techy-robot/CACKLE/Docs/Wiki/media/ESP32-S3.png

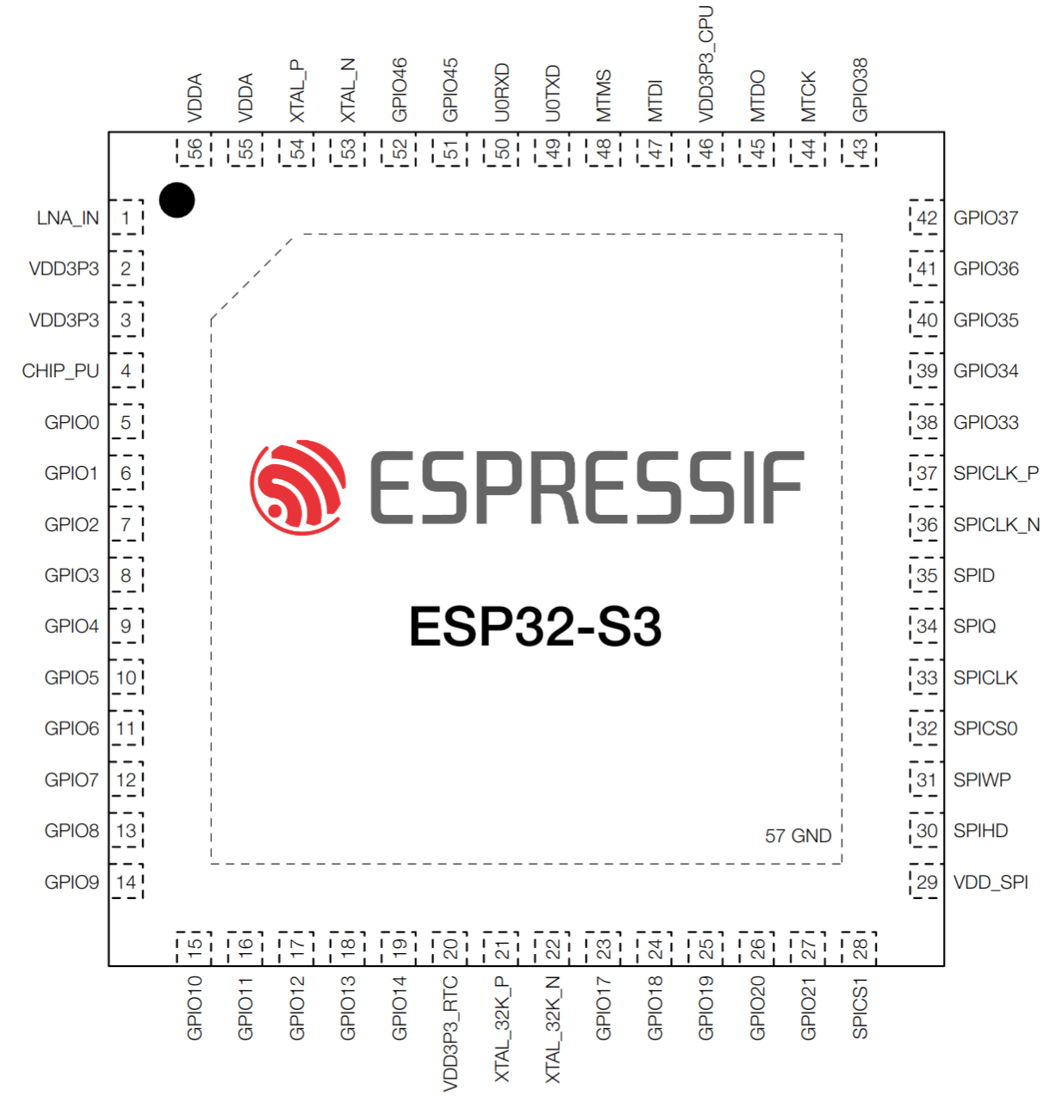
Docs/Wiki/media/ESP32-S3.png
