techy-robot/CACKLE/Docs/Wiki/media/STM32G0B1KCUx.jpg

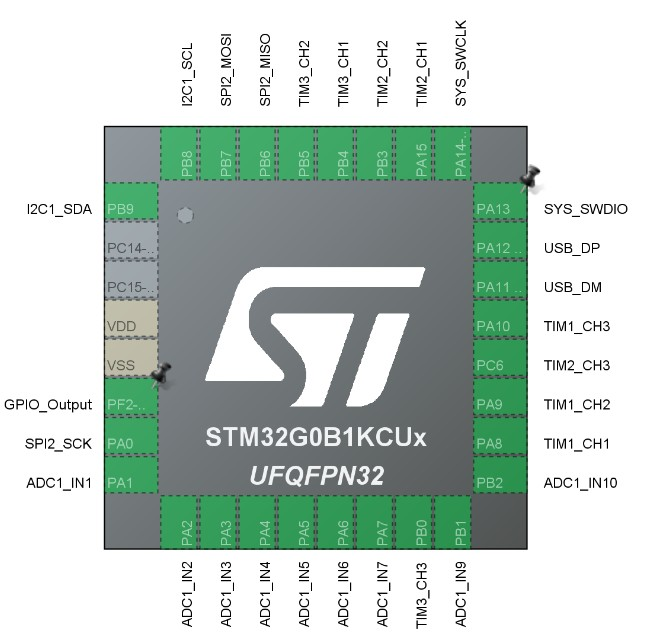
Docs/Wiki/media/STM32G0B1KCUx.jpg
