techy-robot/CACKLE/Docs/Wiki/media/STM32G070CB.jpg

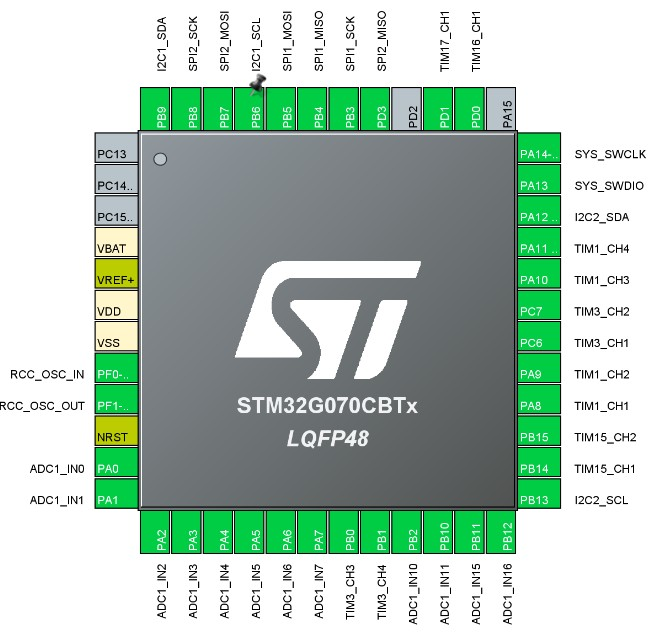
Docs/Wiki/media/STM32G070CB.jpg
