techy-robot/CACKLE/Docs/Wiki/media/STM32G070KB.jpg

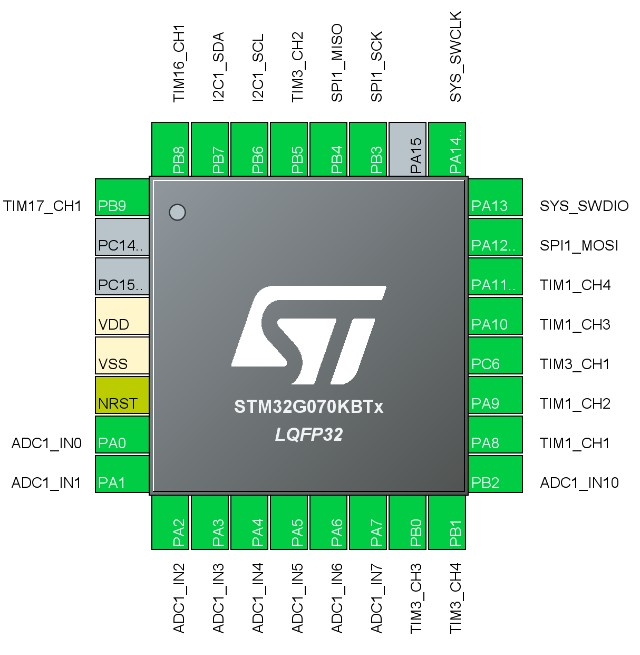
Docs/Wiki/media/STM32G070KB.jpg
