techy-robot/CACKLE/Docs/Wiki/media/STM32G473CB.jpg

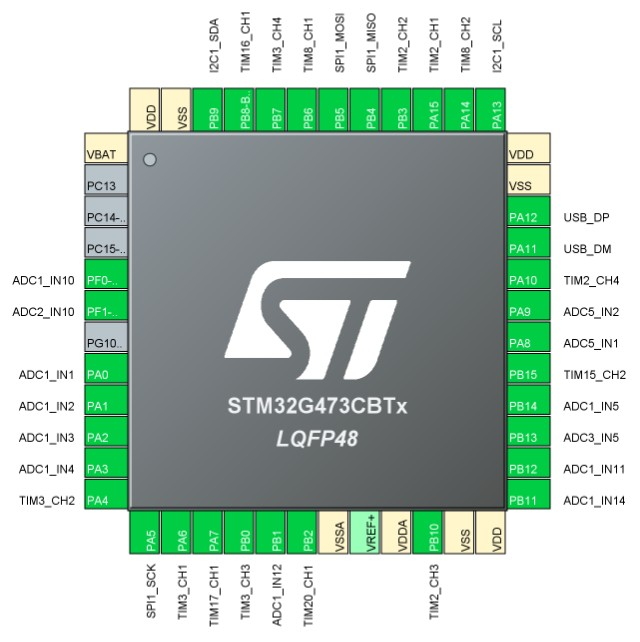
Docs/Wiki/media/STM32G473CB.jpg
