techy-robot/CACKLE/Docs/Wiki/media/STM32G474RC.jpg

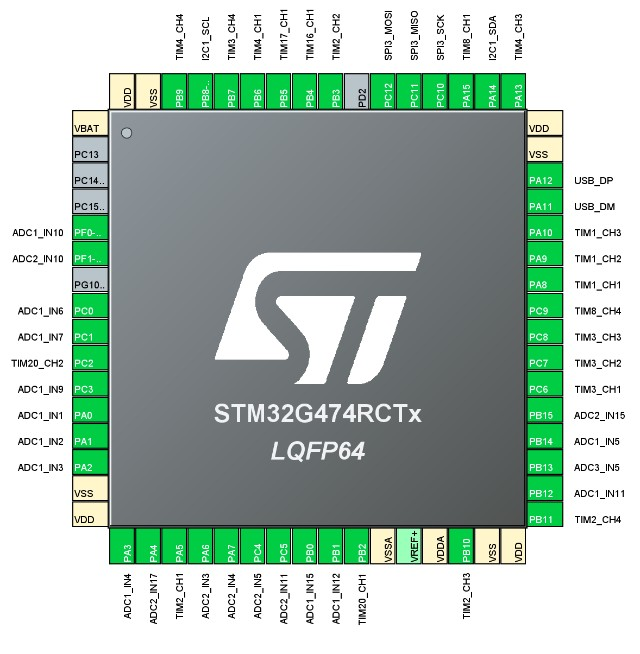
Docs/Wiki/media/STM32G474RC.jpg
