techy-robot/CACKLE/Hardware/Drivers/DRV8213 brushed Motor Driver/media/DRV8213 3D model picture.jpg

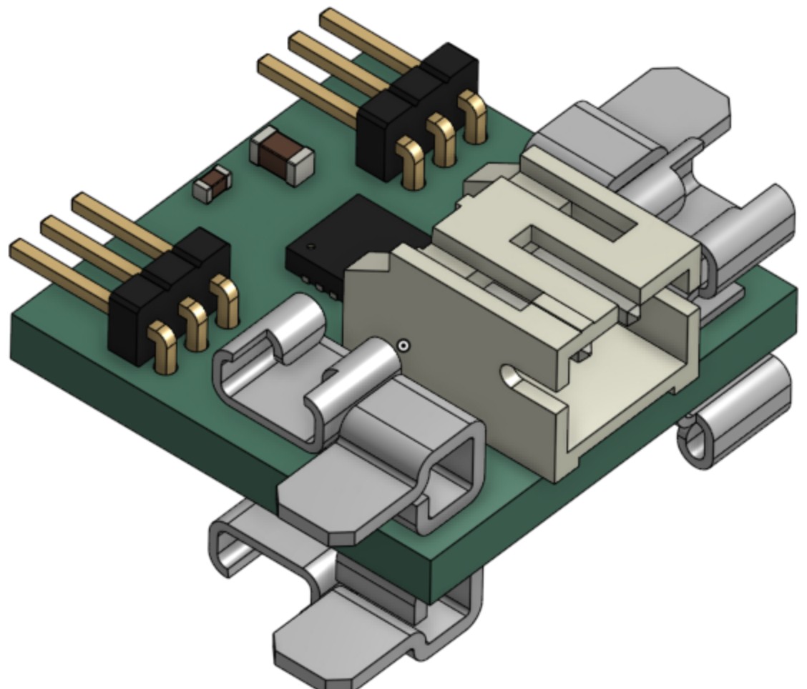
Hardware/Drivers/DRV8213 brushed Motor Driver/media/DRV8213 3D model picture.jpg
