techy-robot/CACKLE/Hardware/Drivers/DRV8213 brushed Motor Driver/media/DRV8213 Bottom.png

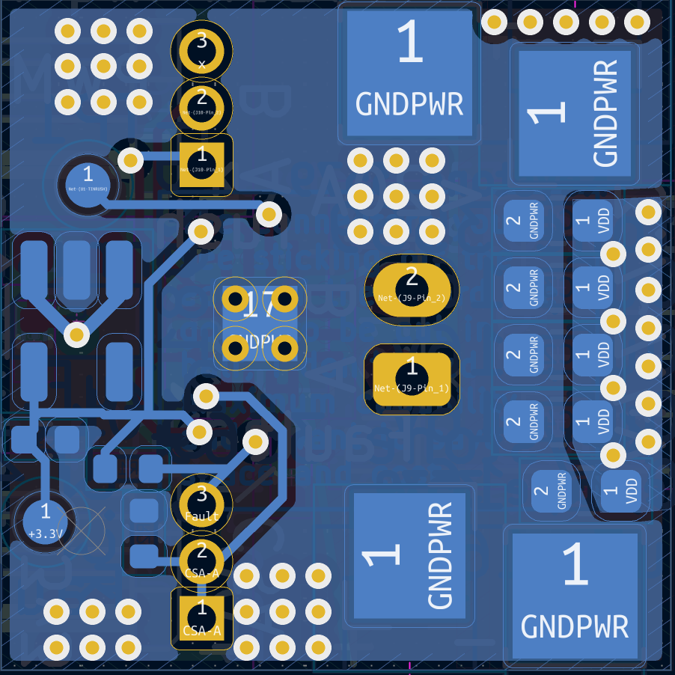
Hardware/Drivers/DRV8213 brushed Motor Driver/media/DRV8213 Bottom.png
