techy-robot/CACKLE/Hardware/Drivers/DRV8311 Motor Driver/media/DRV8311 3D model picture.jpg

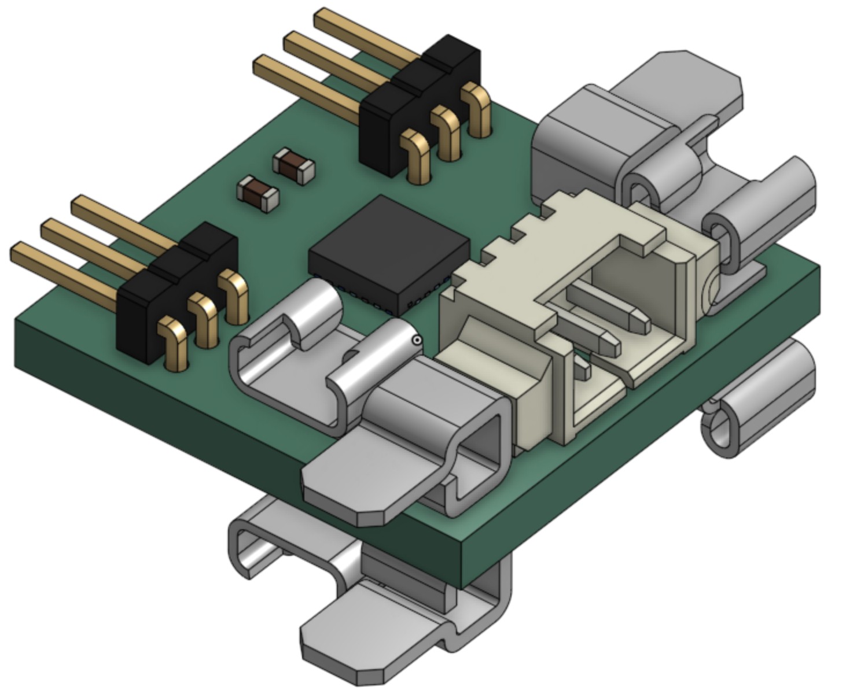
Hardware/Drivers/DRV8311 Motor Driver/media/DRV8311 3D model picture.jpg
