techy-robot/CACKLE/Hardware/Expansion cards/2 connector Sensor Board/media/2 conn Sensor Board Bottom.png

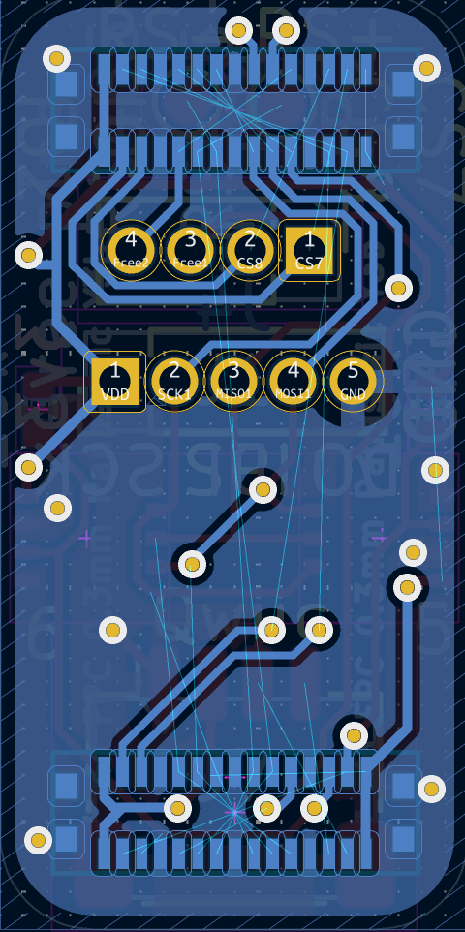
Hardware/Expansion cards/2 connector Sensor Board/media/2 conn Sensor Board Bottom.png
