techy-robot/CACKLE/Hardware/Expansion cards/2 connector Sensor Board/media/2 conn Sensor Board Top.png

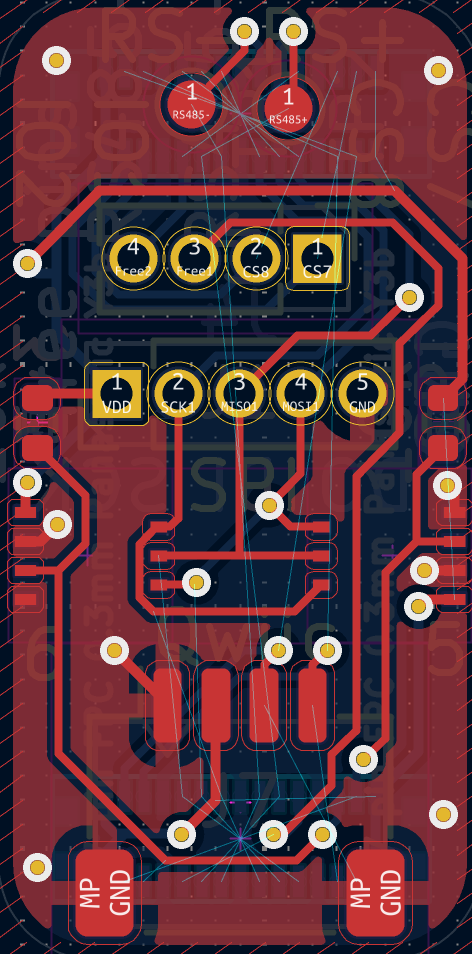
Hardware/Expansion cards/2 connector Sensor Board/media/2 conn Sensor Board Top.png
