techy-robot/CACKLE/Hardware/Hubs/ESP32-S3 Hub/media/Esp32-s3 hub 3D picture.png

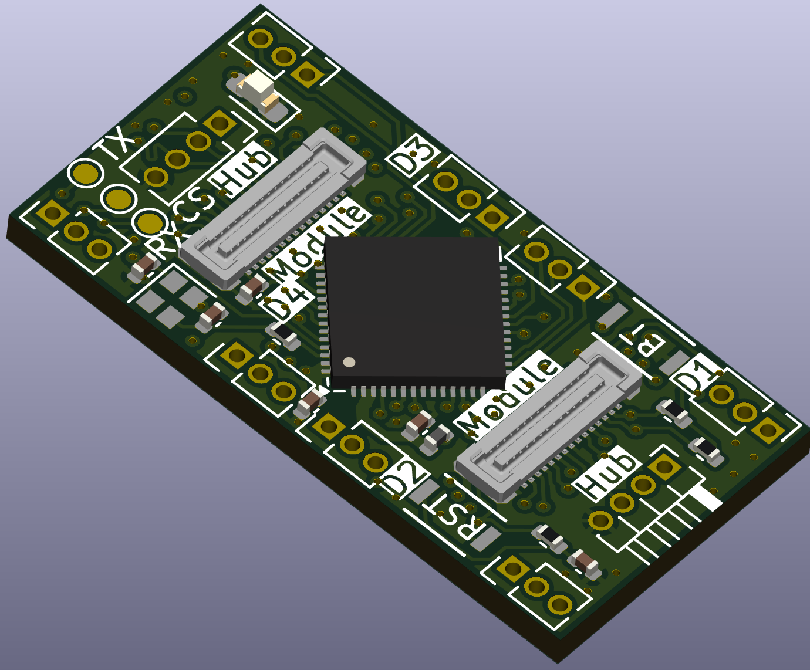
Hardware/Hubs/ESP32-S3 Hub/media/Esp32-s3 hub 3D picture.png
