techy-robot/CACKLE/Hardware/Hubs/ESP32-S3 Hub/media/ESP32-S3 hub In4.png

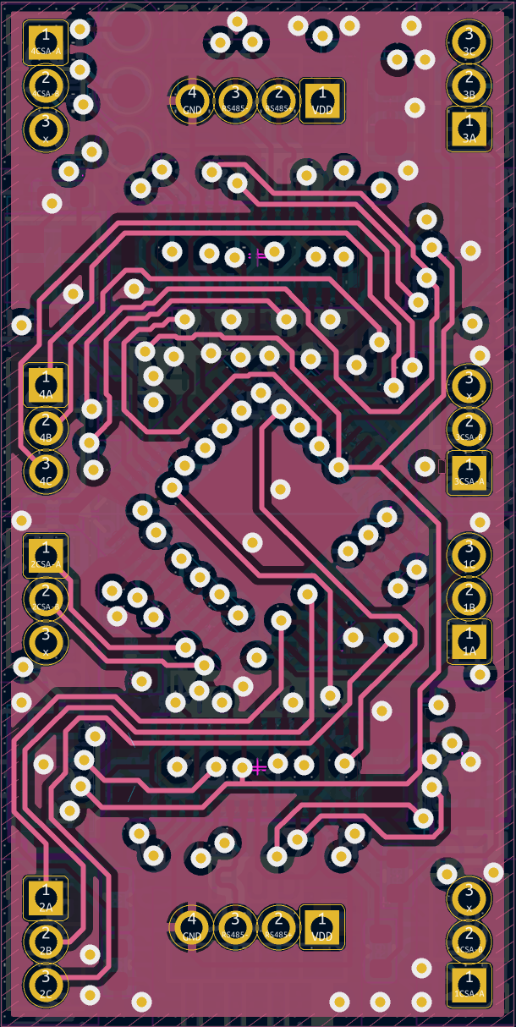
Hardware/Hubs/ESP32-S3 Hub/media/ESP32-S3 hub In4.png
