techy-robot/CACKLE/Hardware/nanoSPI Devices/MA735 magnetic encoder 100mm/media/MA735 Bottom.png

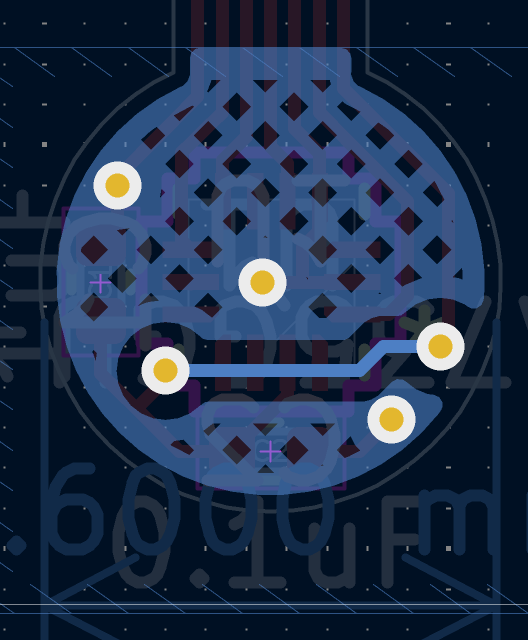
Hardware/nanoSPI Devices/MA735 magnetic encoder 100mm/media/MA735 Bottom.png
