techy-robot/CACKLE/Hardware/nanoSPI Devices/MA735 magnetic encoder 100mm/media/nanoSPI cable connector.png

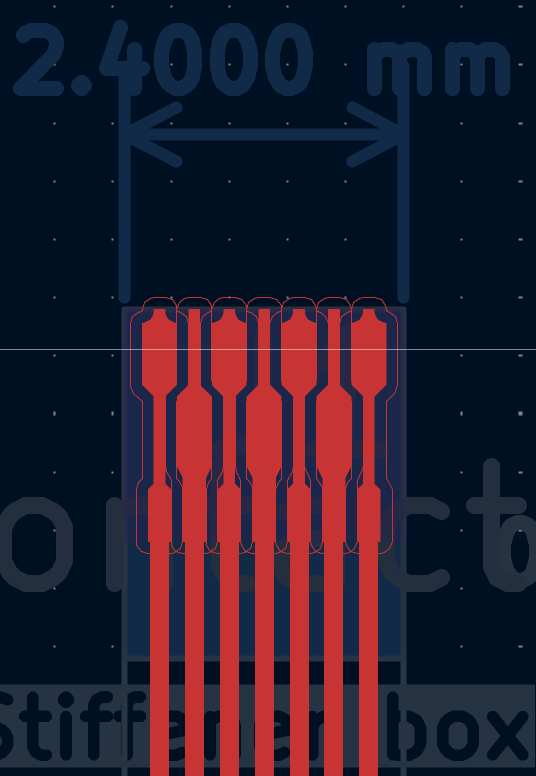
Hardware/nanoSPI Devices/MA735 magnetic encoder 100mm/media/nanoSPI cable connector.png
