techy-robot/CACKLE/Hardware/PSUs/2s 40A PSU and charger/media/2s 40a PSU In2.png

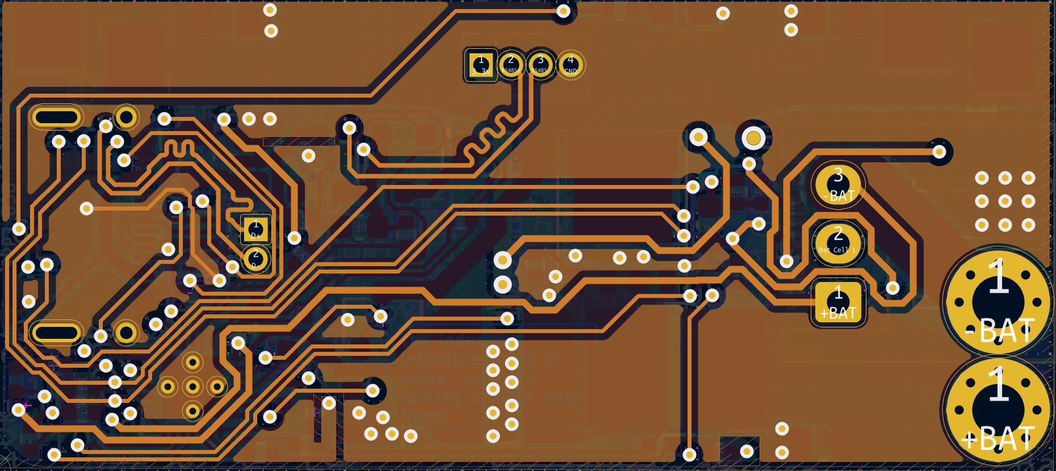
Hardware/PSUs/2s 40A PSU and charger/media/2s 40a PSU In2.png
