techy-robot/CACKLE/Hardware/PSUs/2s 40A PSU and charger/media/2s 40a PSU Top.png

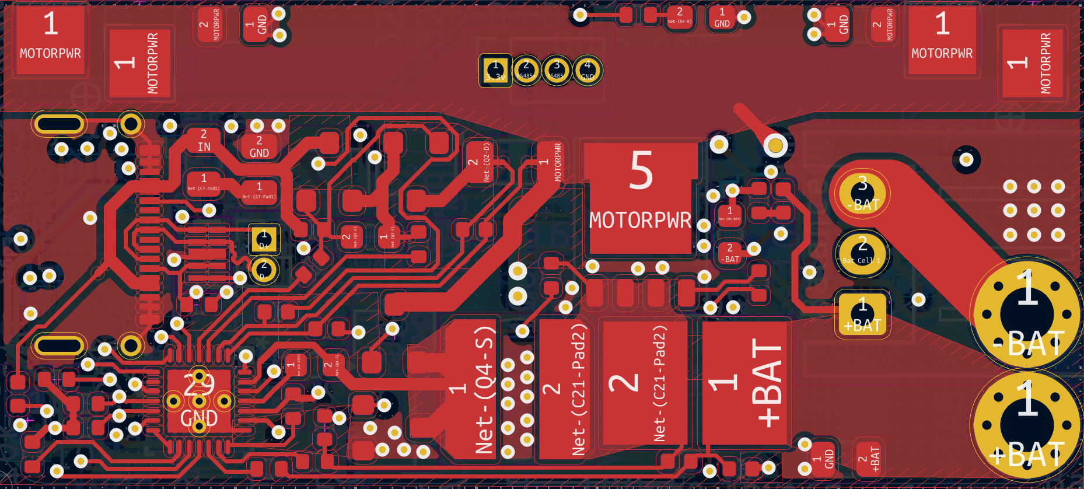
Hardware/PSUs/2s 40A PSU and charger/media/2s 40a PSU Top.png
