techy-robot/CACKLE/media/CACKLE 3D model demo side view.png

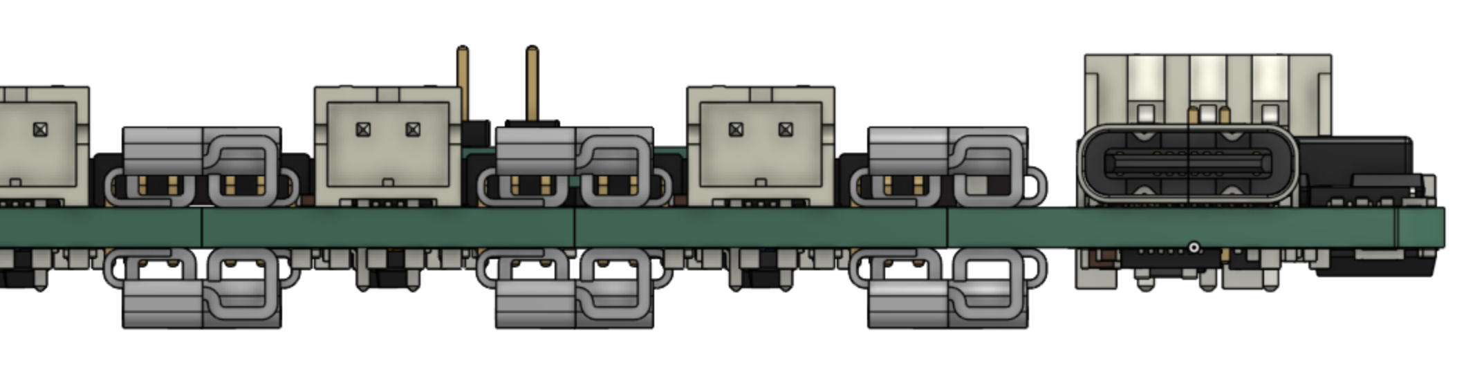
media/CACKLE 3D model demo side view.png
