techy-robot/CACKLE/Hardware/nanoSPI Devices/MA735 magnetic encoder 100mm/production/Proto 1/bom.csv

Designator | Footprint | Quantity | Value | LCSC Part #
C1 | 0402 | 1 | 1uF | C52923
C2 | 0402 | 1 | 0.1uF | C1525
U1 | UTQFN-14_MA735_MNP | 1 | MA735GGU-Z | C17233427
