techy-robot/CACKLE/Hardware/Passive Boards/End Cap/production/Proto 1/bom.csv

Designator | Footprint | Quantity | Value | LCSC Part #
R1 | 0402 | 1 | 120ohm | C25079
TP3 | TestPoint_Pad_D1.0mm | 1 | 3.3v
TP4 | TestPoint_Pad_D1.0mm | 1 | GND
